fhb/FSR-bed-sensor-Lolin-ESP32-C3/PCB/V2/IMG_0450.PNG

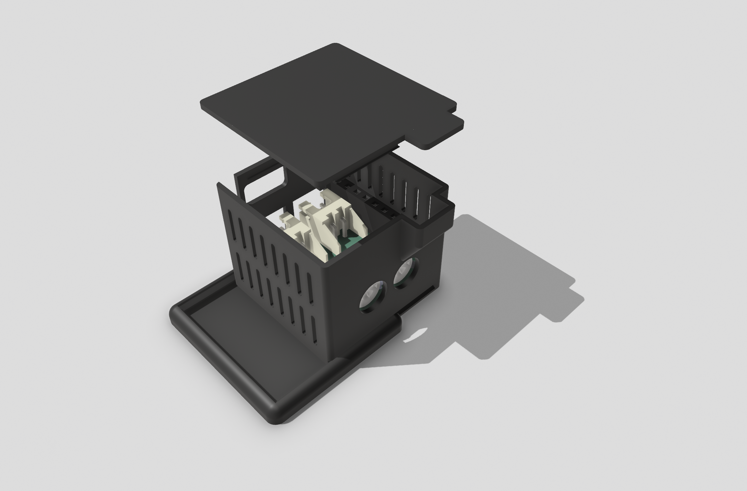
PCB/V2/IMG_0450.PNG
